Benas09/FujitsuAC/src/NetworkUpdater.h

/*
  FujitsuAC - ESP32 libary for controlling FujitsuAC through MQTT
  Copyright (c) 2025 Benas Ragauskas. All rights reserved.
  
  Project home: https://github.com/Benas09/FujitsuAC
*/

#pragma once

//Version check
#include "esp_chip_info.h"
#include <lwip/apps/sntp.h>
#include <WiFiClientSecure.h>

//OTA
#include <HTTPClient.h>
#include <HTTPUpdate.h>

namespace FujitsuAC {
	enum class TimeState {
	    WAITING_INITIALIZATION,
	    INITIATED,
	    SYNCED,
	    ERROR
	};

	enum class VersionCheckerState {
	    WAITING_TIME,
	    TIME_OBTAINED,
	    HTTPS_DOWNLOADING,
	    VERSION_CHECKED,
	    ERROR
	};

    class NetworkUpdater {
    	public:
    		NetworkUpdater();

            void loop();
	        void updateFirmware(const char *branch);
	        
	        void setOnVersionReceivedCallback(std::function<void(const char*)> onVersionReceivedCallback) {
	        	this->onVersionReceivedCallback = onVersionReceivedCallback;
	        }

	        void setDebugCallback(std::function<void(const char* name, const char* message)> debugCallback) {
	        	this->debugCallback = debugCallback;
	        }

        private:
        	WiFiClientSecure* _client = nullptr;

        	TimeState _timeState = TimeState::WAITING_INITIALIZATION;
        	uint32_t _timeCheckInitiatedAtMillis = 0;

        	VersionCheckerState _versionCheckerState = VersionCheckerState::WAITING_TIME;
        	uint32_t _lastVersionCheckInitiatedAtMillis = 0;

        	std::function<void(const char*)> onVersionReceivedCallback;
        	std::function<void(const char* name, const char* message)> debugCallback;

			const char *rootCACertificate = R"string_literal(
-----BEGIN CERTIFICATE-----
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
-----END CERTIFICATE-----
				)string_literal";

			void setClock();
			void requestVersion();
			void debug(const char* name, const char* message);
			void debugTime(time_t nowSecs);
    };
}
